Jozko-Mrkvicka/RadioStack/Software_AVR/modules/navcom.c

/*************************************************************
* RadioStack v2.0/navcom
*************************************************************/
#include "navcom.h"

static void navcomm_input_convert_button_data(uint8_t gp_reg, uint8_t *button);
static void navcomm_input_convert_encoder_data(uint8_t intcap_reg, uint8_t gp_reg, uint8_t *encoder);


void navcomm_output(uint8_t* str_1,
					uint8_t* str_2,
					uint8_t* str_3,
					uint8_t* str_4,
					uint8_t* led,
					uint8_t address)
{
	uint8_t message[DIPLAY_DRIVER_MESSAGE_SIZE];

	uint8_t str_1_converted[NAVCOMM_STRING_LEN];
	uint8_t str_2_converted[NAVCOMM_STRING_LEN];
	uint8_t str_3_converted[NAVCOMM_STRING_LEN];
	uint8_t str_4_converted[NAVCOMM_STRING_LEN];
	uint8_t led_converted[NAVCOMM_LED_NUM];

	uint8_t data_1[DIPLAY_DRIVER_DATA_SIZE];
	uint8_t data_2[DIPLAY_DRIVER_DATA_SIZE];
	uint8_t data_3[DIPLAY_DRIVER_DATA_SIZE];

	icm7228_convert_char_to_code(str_1, str_1_converted, NAVCOMM_STRING_LEN);
	icm7228_convert_char_to_code(str_2, str_2_converted, NAVCOMM_STRING_LEN);
	icm7228_convert_char_to_code(str_3, str_3_converted, NAVCOMM_STRING_LEN);
	icm7228_convert_char_to_code(str_4, str_4_converted, NAVCOMM_STRING_LEN);
	icm7228_convert_char_to_code(led,   led_converted,   NAVCOMM_LED_NUM);

	data_1[0u] = str_1_converted[0u];  /* "COMM USE"  */ 
	data_1[1u] = str_1_converted[1u];  /* "COMM USE"  */ 
	data_1[2u] = str_1_converted[2u];  /* "COMM USE"  */ 
	data_1[3u] = str_1_converted[3u];  /* "COMM USE"  */ 
	data_1[4u] = str_1_converted[4u];  /* "COMM USE"  */ 
	data_1[5u] = str_2_converted[0u];  /* "COMM STBY" */ 
	data_1[6u] = str_2_converted[1u];  /* "COMM STBY" */ 
	data_1[7u] = str_2_converted[2u];  /* "COMM STBY" */ 

	data_2[0u] = str_2_converted[3u];  /* "COMM STBY" */ 
	data_2[1u] = str_2_converted[4u];  /* "COMM STBY" */ 
	data_2[2u] = str_3_converted[0u];  /* "NAV USE"   */ 
	data_2[3u] = str_3_converted[1u];  /* "NAV USE"   */ 
	data_2[4u] = str_3_converted[2u];  /* "NAV USE"   */ 
	data_2[5u] = str_3_converted[3u];  /* "NAV USE"   */ 
	data_2[6u] = str_3_converted[4u];  /* "NAV USE"   */ 
	data_2[7u] = str_4_converted[0u];  /* "NAV STBY"  */ 

	data_3[0u] = str_4_converted[1u];  /* "NAV STBY"  */ 
	data_3[1u] = str_4_converted[2u];  /* "NAV STBY"  */ 
	data_3[2u] = str_4_converted[3u];  /* "NAV STBY"  */ 
	data_3[3u] = str_4_converted[4u];  /* "NAV STBY"  */ 
	data_3[4u] = led_converted[0u];    /* "TEST LED"  */
	data_3[5u] = led_converted[1u];    /* "IDENT LED" */
	data_3[6u] = CHAR_BLANK;           /* Not used.   */
	data_3[7u] = CHAR_BLANK;           /* Not used.   */

	icm7228_create_message(message, data_1, DRIVER_1_WRITE_HIGH);
	twi_transmit_data(message, DIPLAY_DRIVER_MESSAGE_SIZE, address);

	icm7228_create_message(message, data_2, DRIVER_2_WRITE_HIGH);
	twi_transmit_data(message, DIPLAY_DRIVER_MESSAGE_SIZE, address);

	icm7228_create_message(message, data_3, DRIVER_3_WRITE_HIGH);
	twi_transmit_data(message, DIPLAY_DRIVER_MESSAGE_SIZE, address);
}


uint8_t navcomm_input(uint8_t address, uint8_t* encoder, uint8_t* button)
{
	uint8_t twi_status = 0xFFu;

	uint8_t gp_reg[2u];
	uint8_t intcap_reg[2u];

	twi_status = mcp23016_read_input(gp_reg,     address, ACCESS_TO_GP0);
	twi_status = mcp23016_read_input(intcap_reg, address, ACCESS_TO_INTCAP0);

	navcomm_input_convert_encoder_data(intcap_reg[1u], gp_reg[0u], encoder);
	navcomm_input_convert_button_data(gp_reg[0u], button);

	return twi_status;
}


/* This function inputs two bytes of read data from I2C expander and converts
   it to an array of four integers. Each integer has one of three values 
   to indicate encoder motion (0 == no change, 1 == turn left, 2 == turn right). */
static void navcomm_input_convert_encoder_data(uint8_t intcap_reg, uint8_t gp_reg, uint8_t* encoder)
{
	uint8_t clk[ENC_NUM];
	uint8_t updn[ENC_NUM];

	clk[0u] = ((intcap_reg & 0x01u) >> 0u);
	clk[1u] = ((intcap_reg & 0x02u) >> 1u);
	clk[2u] = ((intcap_reg & 0x04u) >> 2u);
	clk[3u] = ((intcap_reg & 0x08u) >> 3u);

	updn[0u] = ((gp_reg & 0x01u) >> 0u);
	updn[1u] = ((gp_reg & 0x02u) >> 1u);
	updn[2u] = ((gp_reg & 0x04u) >> 2u);
	updn[3u] = ((gp_reg & 0x08u) >> 3u);

	for (uint8_t i = 0u; i < ENC_NUM; i++)
	{
		encoder[i] = 0u;
		if (0u == clk[i])
		{
			if (updn[i])
				encoder[i] = ENC_ROT_LEFT;
			else
				encoder[i] = ENC_ROT_RIGHT;
		}
	}
}


static void navcomm_input_convert_button_data(uint8_t gp_reg, uint8_t* button)
{
	button[0u] = ((gp_reg & 0x10u) >> 4u);
	button[1u] = ((gp_reg & 0x20u) >> 5u);
	button[2u] = ((gp_reg & 0x40u) >> 6u);
	button[3u] = ((gp_reg & 0x80u) >> 7u);
}
