Jozko-Mrkvicka/RadioStack/Software_AVR/modules/includes/navcom.h

#ifndef __NAVCOM__
#define __NAVCOM__

#include <stdio.h>

#include "../../common/includes/icm7228.h"
#include "../../common/includes/two_wire_interface.h"
#include "../../common/includes/mcp23016.h"

/* Number of rotary encoders in NavCom module. */
#define ENC_NUM  4u

#define NAVCOMM_LED_NUM  2u

#define ENC_ROT_NONE   0u
#define ENC_ROT_LEFT   1u
#define ENC_ROT_RIGHT  2u

#define DRIVER_1_WRITE_HIGH  0x20u
#define DRIVER_2_WRITE_HIGH  0x40u
#define DRIVER_3_WRITE_HIGH  0x80u

void navcomm_output(uint8_t* str_1,
					uint8_t* str_2,
					uint8_t* str_3,
					uint8_t* str_4,
					uint8_t* led,
					uint8_t address);

uint8_t navcomm_input(uint8_t address, uint8_t* encoder, uint8_t* button);

#endif
